jonathanvanschenck/lesser-magistrate/graphics/main.png

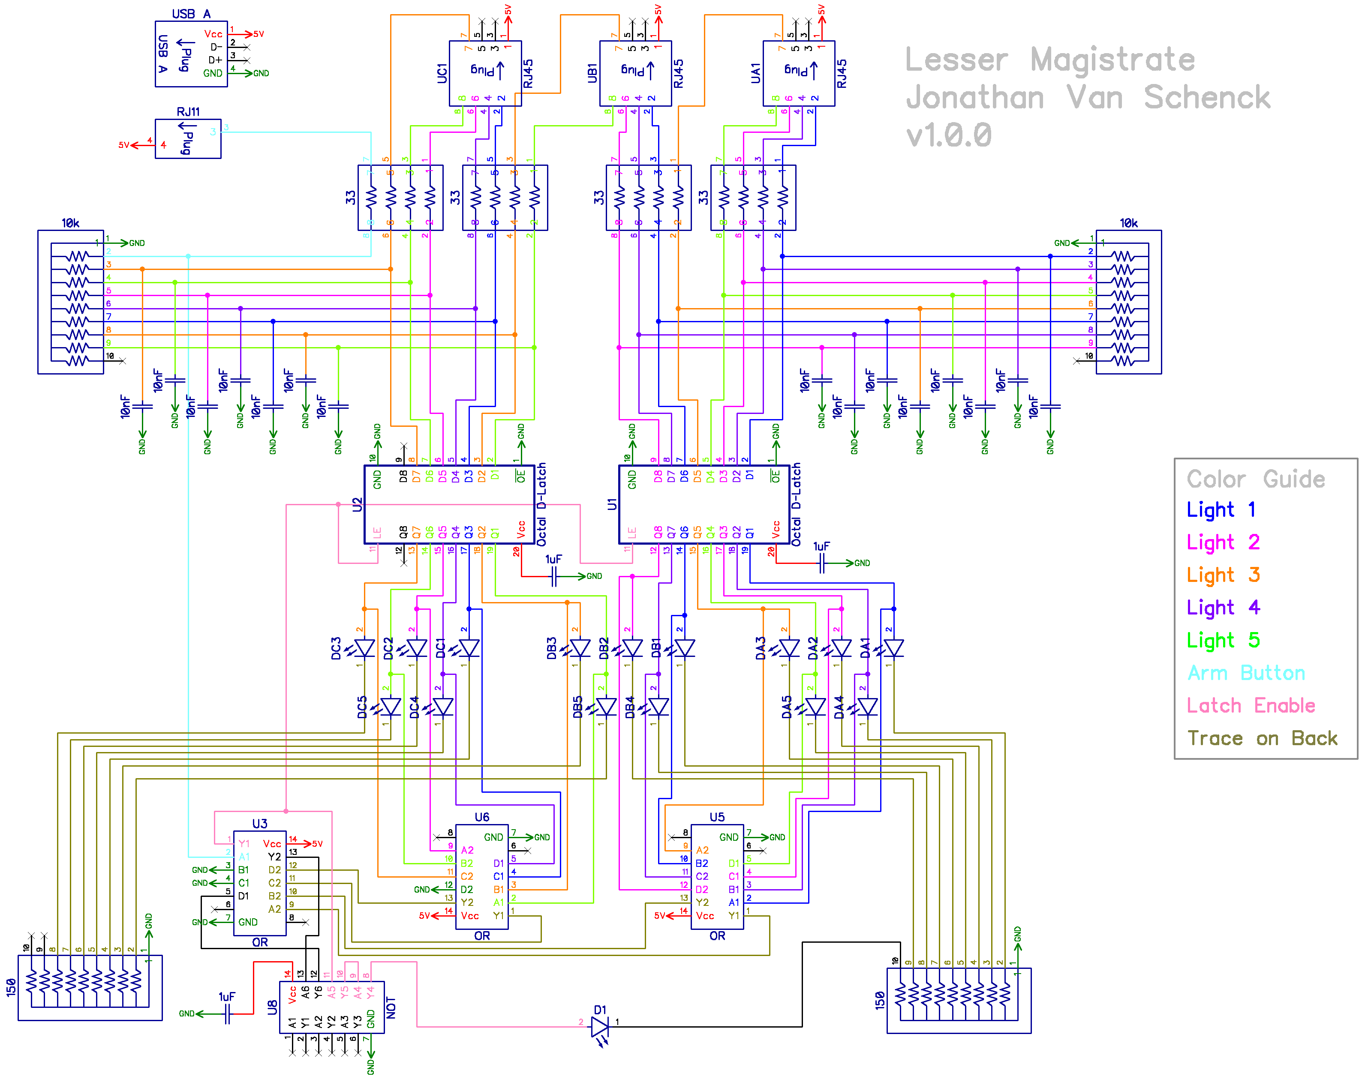
graphics/main.png
