jonathanvanschenck/lesser-magistrate/graphics/module.png

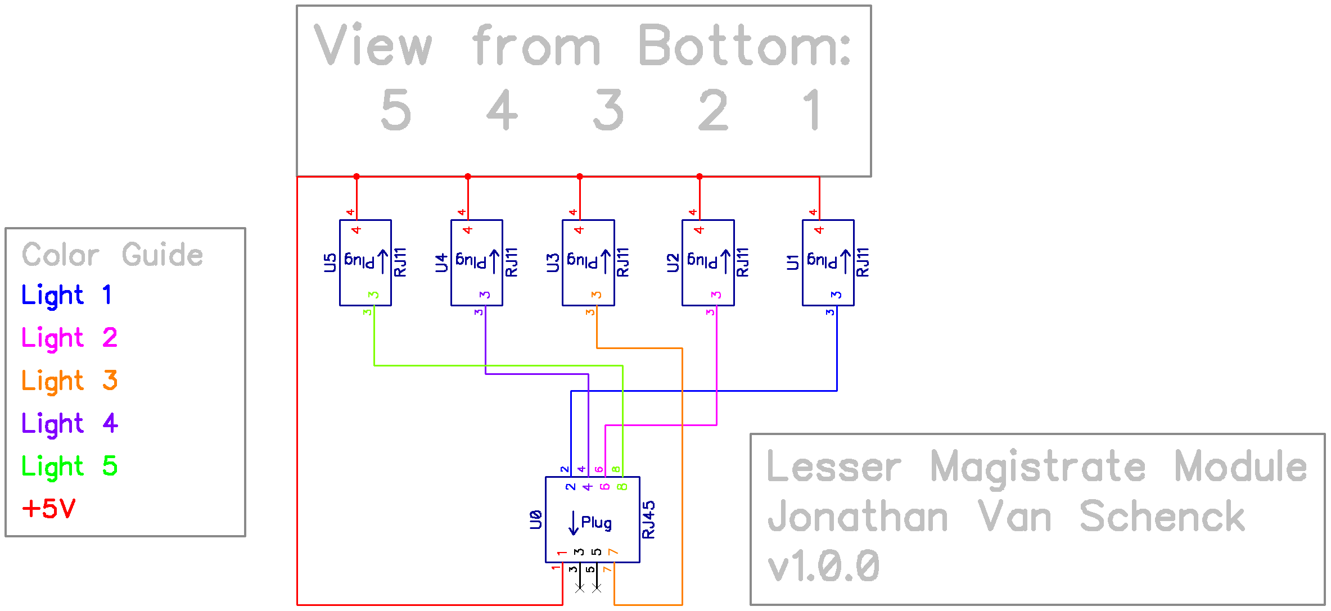
graphics/module.png
