jonathanvanschenck/lesser-magistrate/images/3_lm_console_power.jpg

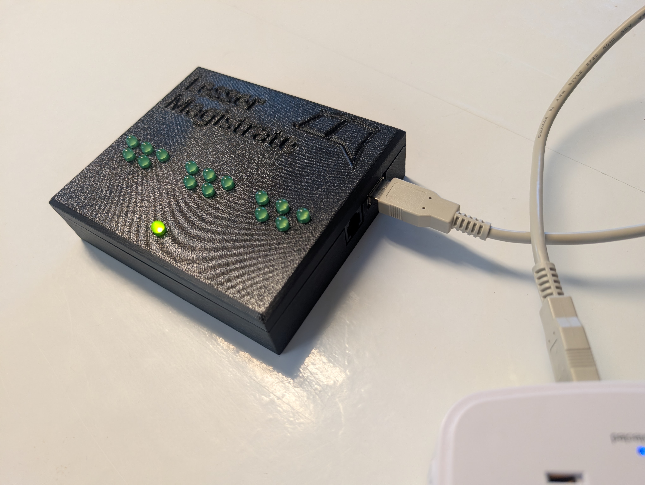
images/3_lm_console_power.jpg
