jonathanvanschenck/lesser-magistrate/images/6_lm_junction.jpg

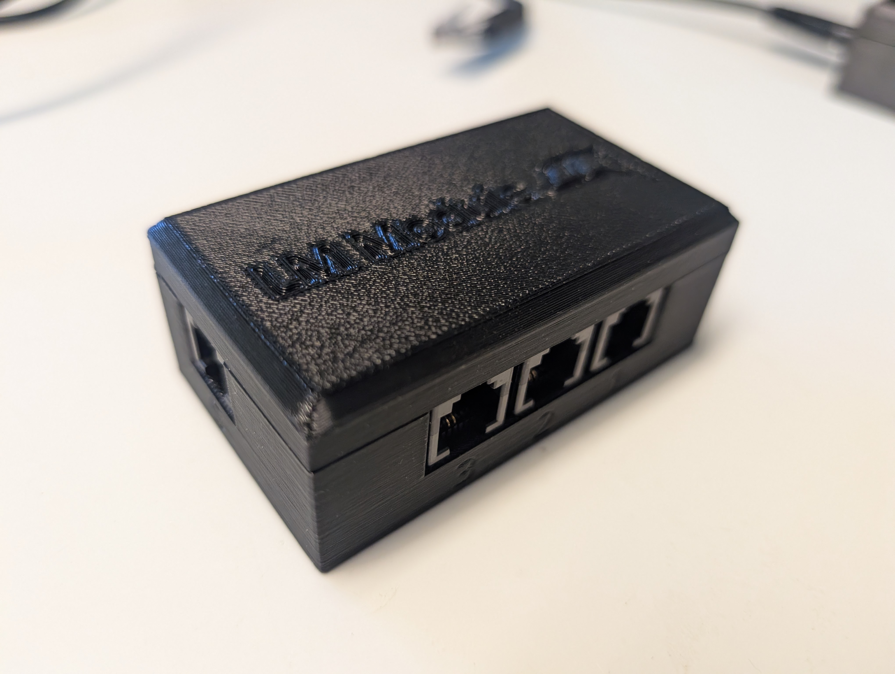
images/6_lm_junction.jpg
