jonathanvanschenck/lesser-magistrate/images/7_lm_junction_plugged.jpg

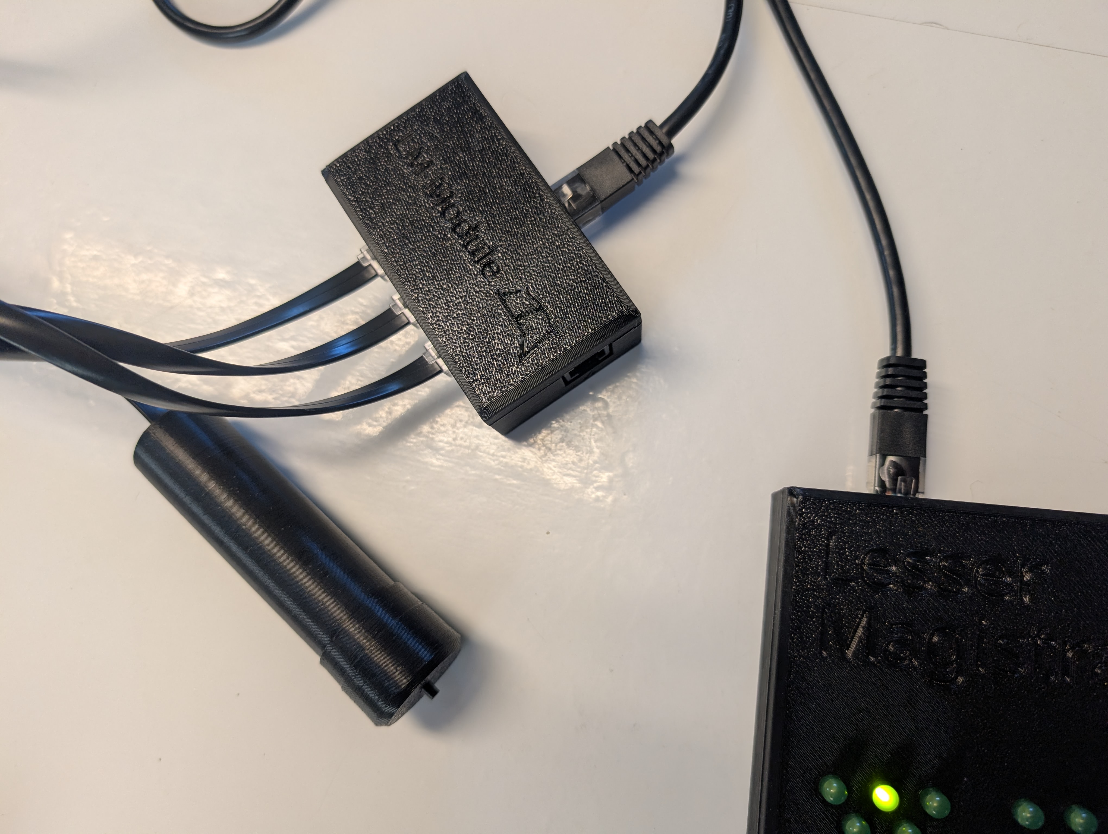
images/7_lm_junction_plugged.jpg
